bachthyaglx/Stable-Gait-Optimization-for-Small-Sized-Humanoid-Robot-Using-CFO/Solidworks/Part22_1.SLDPRT

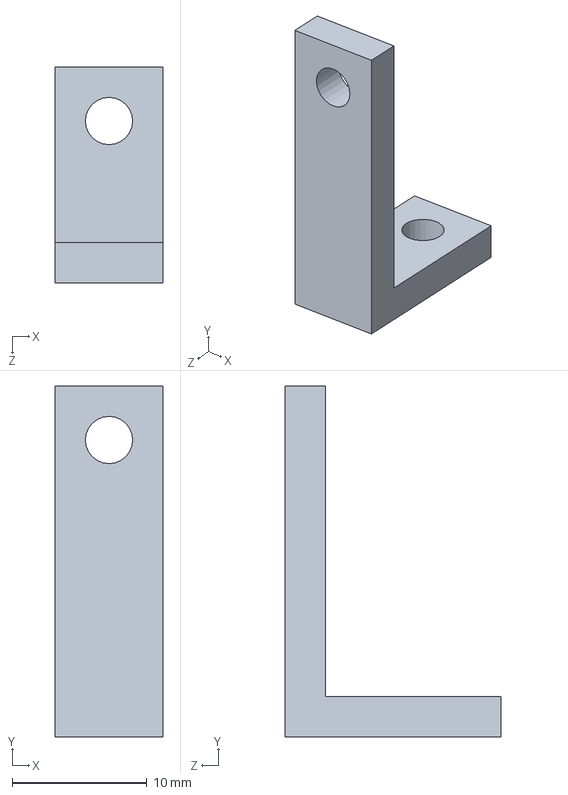
[picture p26: CAD file, 2022-03-02]
Solidworks/Part22_1.SLDPRT
8.00 x 26.0 x 16.0 mm
