bachthyaglx/Stable-Gait-Optimization-for-Small-Sized-Humanoid-Robot-Using-CFO/Solidworks/ArduinoDue/PCB - Arduino.SLDPRT

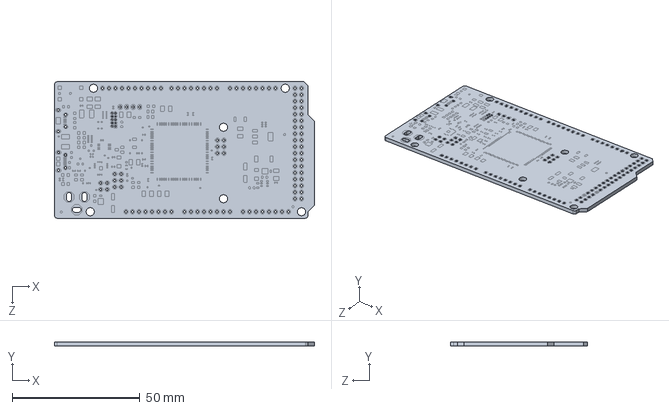
[picture p27: CAD file, 2022-03-02]
Solidworks/ArduinoDue/PCB - Arduino.SLDPRT
101.6 x 1.62 x 53.3 mm
