bachthyaglx/Stable-Gait-Optimization-for-Small-Sized-Humanoid-Robot-Using-CFO/Solidworks/LIPO/NUCLEO.SLDPRT

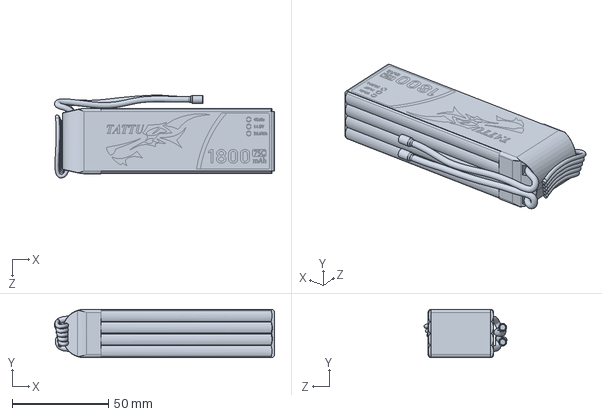
[picture p28: CAD file, 2022-03-02]
Solidworks/LIPO/NUCLEO.SLDPRT
114.2 x 25.0 x 43.0 mm
