bachthyaglx/Stable-Gait-Optimization-for-Small-Sized-Humanoid-Robot-Using-CFO/Solidworks/Part14.SLDPRT

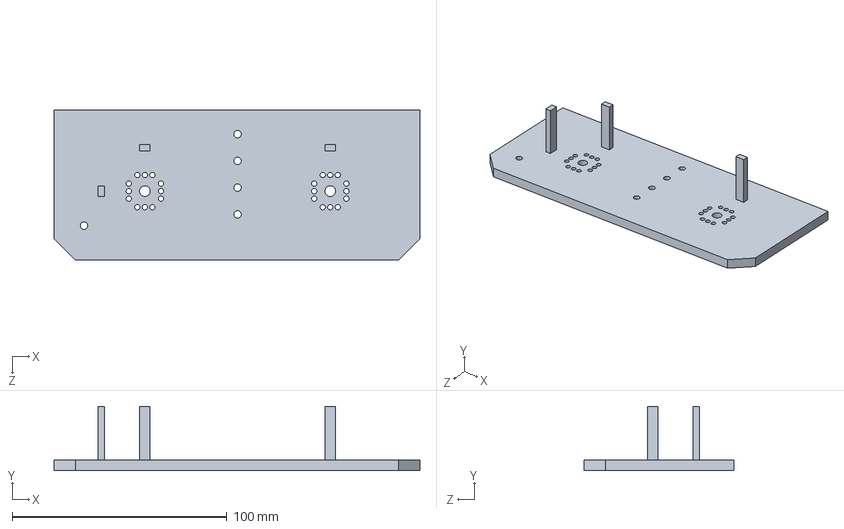
[picture p29: CAD file, 2022-03-02]
Solidworks/Part14.SLDPRT
170.6 x 30.0 x 69.9 mm
