bachthyaglx/Stable-Gait-Optimization-for-Small-Sized-Humanoid-Robot-Using-CFO/Solidworks/LIPO/XT60 Buchse.SLDPRT

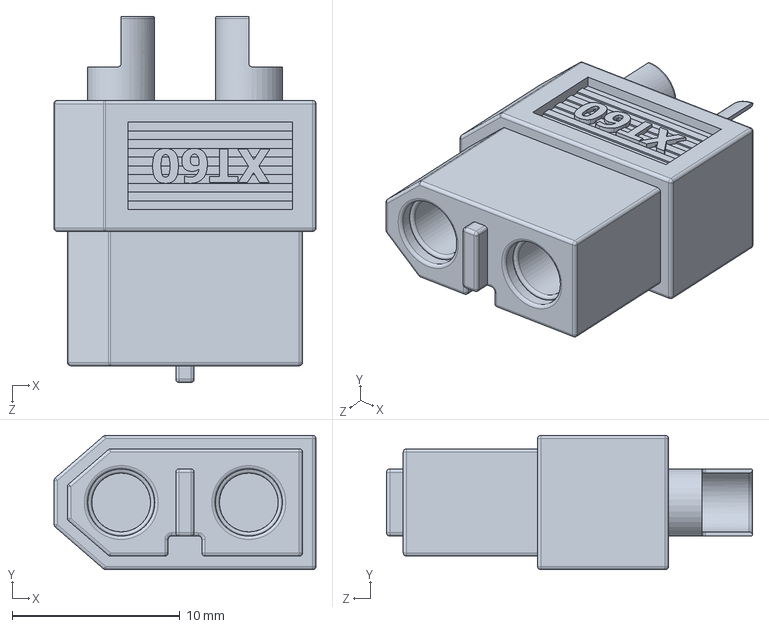
[picture p30: CAD file, 2022-03-02]
Solidworks/LIPO/XT60 Buchse.SLDPRT
15.6 x 8.00 x 21.8 mm
