bachthyaglx/Stable-Gait-Optimization-for-Small-Sized-Humanoid-Robot-Using-CFO/Solidworks/ArduinoDue/Berg Header - 1.27 x 10.SLDPRT

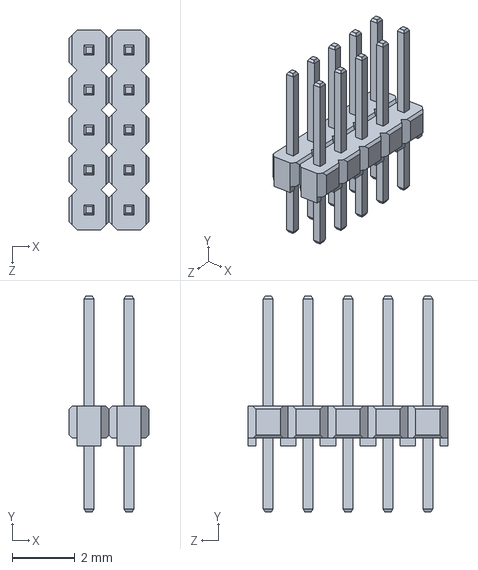
[picture p31: CAD file, 2022-03-02]
Solidworks/ArduinoDue/Berg Header - 1.27 x 10.SLDPRT
2.54 x 6.88 x 6.35 mm
