bachthyaglx/Stable-Gait-Optimization-for-Small-Sized-Humanoid-Robot-Using-CFO/Solidworks/CoDo.SLDPRT

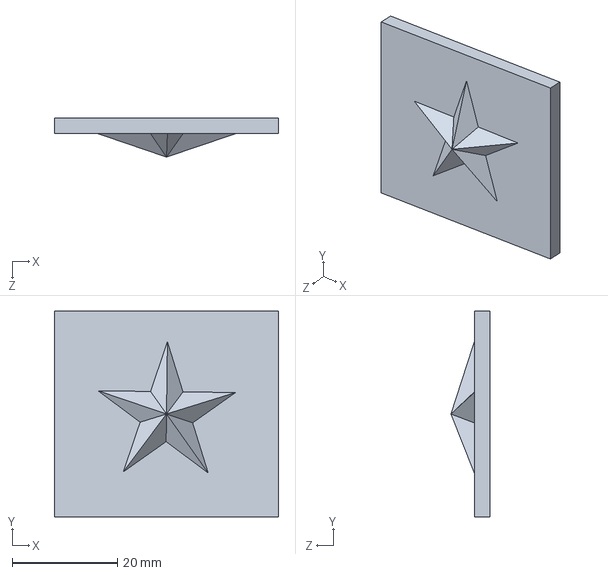
[picture p32: CAD file, 2022-03-02]
Solidworks/CoDo.SLDPRT
42.6 x 39.1 x 7.44 mm
