bachthyaglx/Stable-Gait-Optimization-for-Small-Sized-Humanoid-Robot-Using-CFO/Solidworks/ArduinoDue/MicroUSB AB - Hirose - ZX62D-AB-5P8.SLDPRT

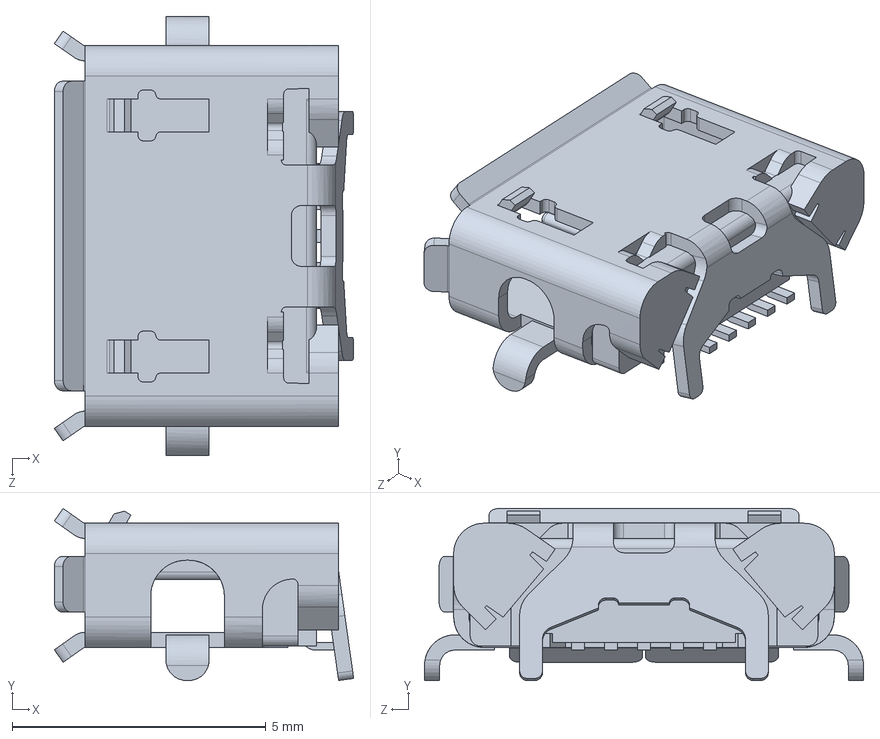
[picture p33: CAD file, 2022-03-02]
Solidworks/ArduinoDue/MicroUSB AB - Hirose - ZX62D-AB-5P8.SLDPRT
5.90 x 3.39 x 8.65 mm
