bachthyaglx/Stable-Gait-Optimization-for-Small-Sized-Humanoid-Robot-Using-CFO/Solidworks/Part15.SLDPRT

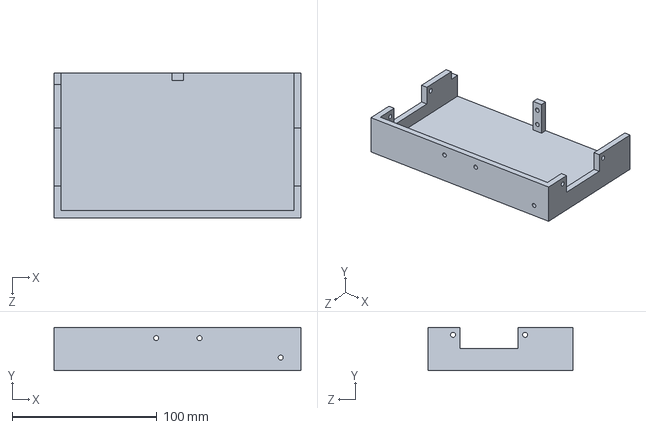
[picture p34: CAD file, 2022-03-02]
Solidworks/Part15.SLDPRT
170.6 x 29.9 x 100.0 mm
