bachthyaglx/Stable-Gait-Optimization-for-Small-Sized-Humanoid-Robot-Using-CFO/Solidworks/ArduinoDue/Capacitor - Nichicon - UUR1C101MCL1GS.SLDPRT

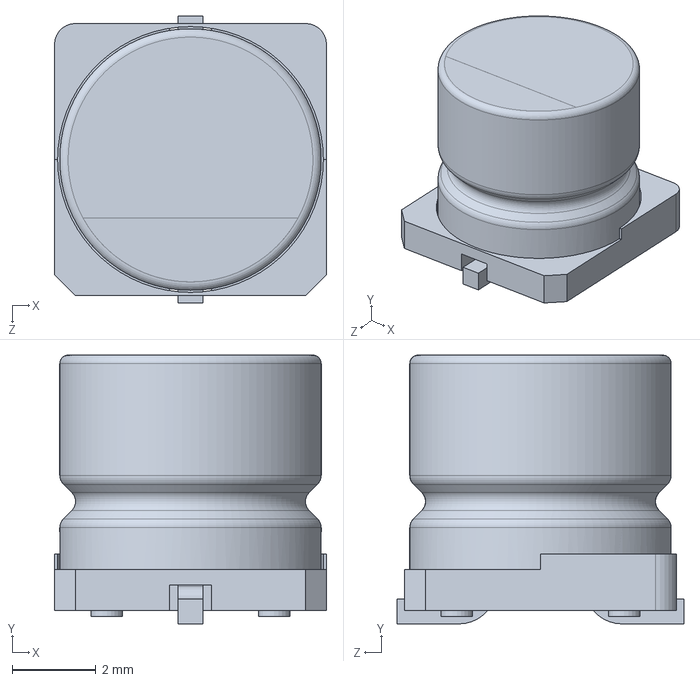
[picture p35: CAD file, 2022-03-02]
Solidworks/ArduinoDue/Capacitor - Nichicon - UUR1C101MCL1GS.SLDPRT
6.50 x 6.42 x 6.85 mm
