bachthyaglx/Stable-Gait-Optimization-for-Small-Sized-Humanoid-Robot-Using-CFO/Solidworks/ArduinoDue/Microchip - Atmel - SAM3X8EAU.SLDPRT

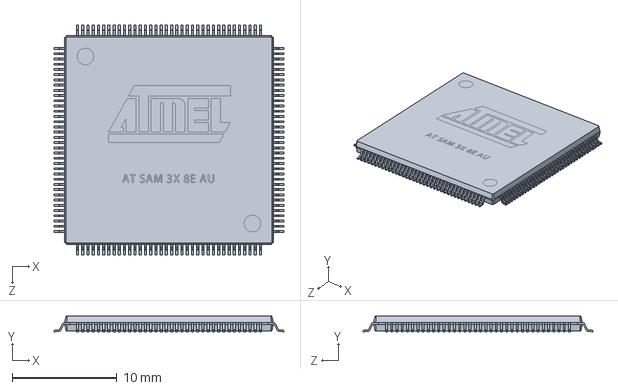
[picture p36: CAD file, 2022-03-02]
Solidworks/ArduinoDue/Microchip - Atmel - SAM3X8EAU.SLDPRT
22.0 x 1.50 x 22.0 mm
