bachthyaglx/Stable-Gait-Optimization-for-Small-Sized-Humanoid-Robot-Using-CFO/Solidworks/Part6.SLDPRT

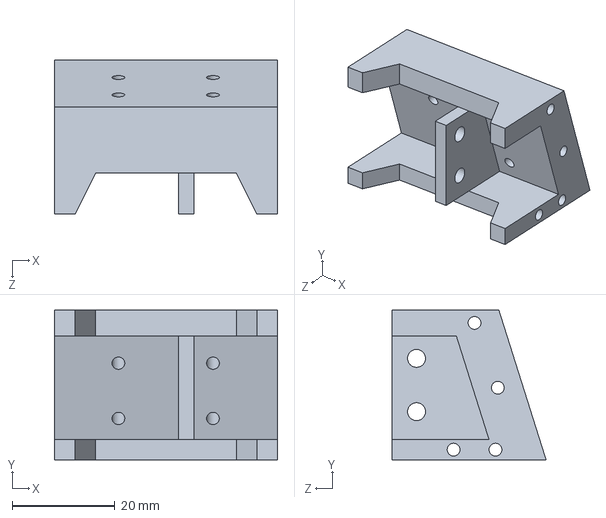
[picture p37: CAD file, 2022-03-02]
Solidworks/Part6.SLDPRT
43.3 x 29.2 x 30.0 mm
