bachthyaglx/Stable-Gait-Optimization-for-Small-Sized-Humanoid-Robot-Using-CFO/Solidworks/ArduinoDue/Power Jack - Kycon - KLDHCX-0202-A.SLDPRT

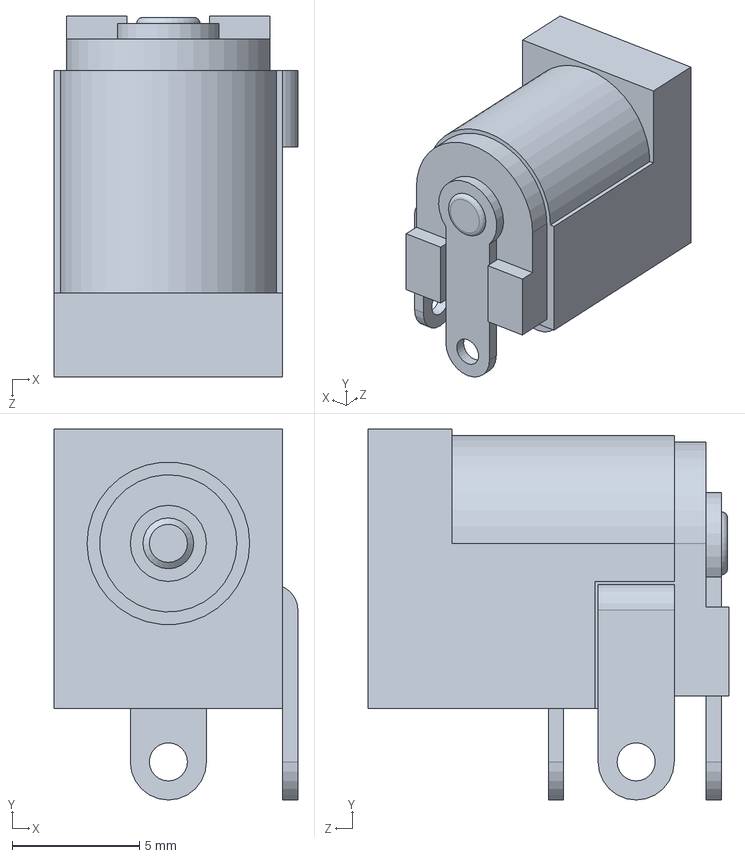
[picture p38: CAD file, 2022-03-02]
Solidworks/ArduinoDue/Power Jack - Kycon - KLDHCX-0202-A.SLDPRT
9.60 x 14.6 x 14.2 mm
