bachthyaglx/Stable-Gait-Optimization-for-Small-Sized-Humanoid-Robot-Using-CFO/Solidworks/ArduinoDue/Berg Header - 2.54 x 2.SLDPRT

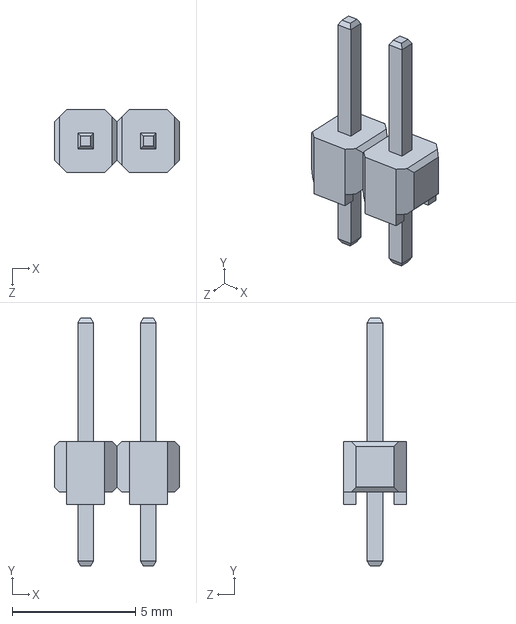
[picture p39: CAD file, 2022-03-02]
Solidworks/ArduinoDue/Berg Header - 2.54 x 2.SLDPRT
5.08 x 10.0 x 2.54 mm
