bachthyaglx/Stable-Gait-Optimization-for-Small-Sized-Humanoid-Robot-Using-CFO/Solidworks/MirrorPart2.SLDPRT

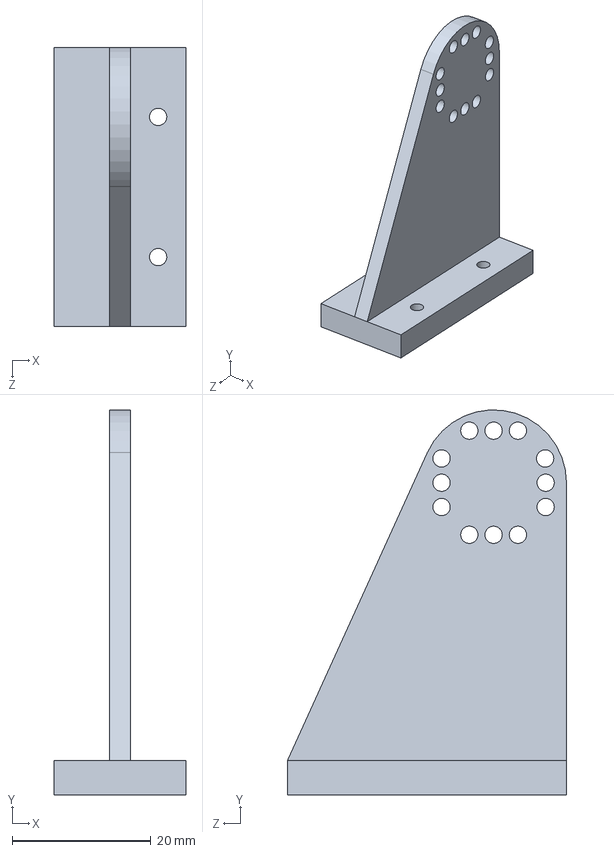
[picture p40: CAD file, 2022-03-02]
Solidworks/MirrorPart2.SLDPRT
19.0 x 55.5 x 40.2 mm
