bachthyaglx/Stable-Gait-Optimization-for-Small-Sized-Humanoid-Robot-Using-CFO/Solidworks/ArduinoDue/LED - Kingbright - KPT-3216EC.SLDPRT

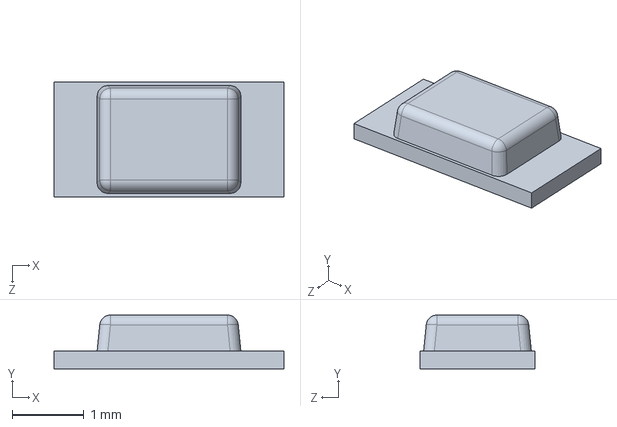
[picture p41: CAD file, 2022-03-02]
Solidworks/ArduinoDue/LED - Kingbright - KPT-3216EC.SLDPRT
3.20 x 0.75 x 1.60 mm
