bachthyaglx/Stable-Gait-Optimization-for-Small-Sized-Humanoid-Robot-Using-CFO/Solidworks/Part21.SLDPRT

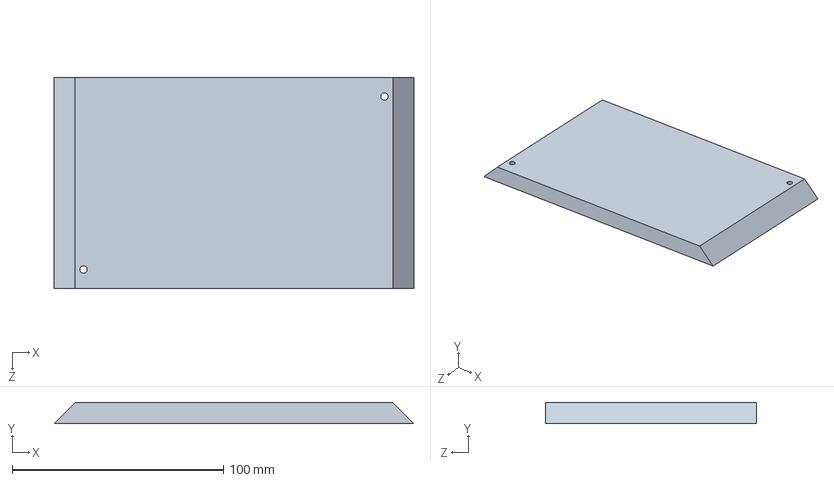
[picture p42: CAD file, 2022-03-02]
Solidworks/Part21.SLDPRT
170.6 x 10.0 x 100.0 mm
