bachthyaglx/Stable-Gait-Optimization-for-Small-Sized-Humanoid-Robot-Using-CFO/Solidworks/ArduinoDue/MicroUSB AB - Hirose - ZX62-AB-5PA.SLDPRT

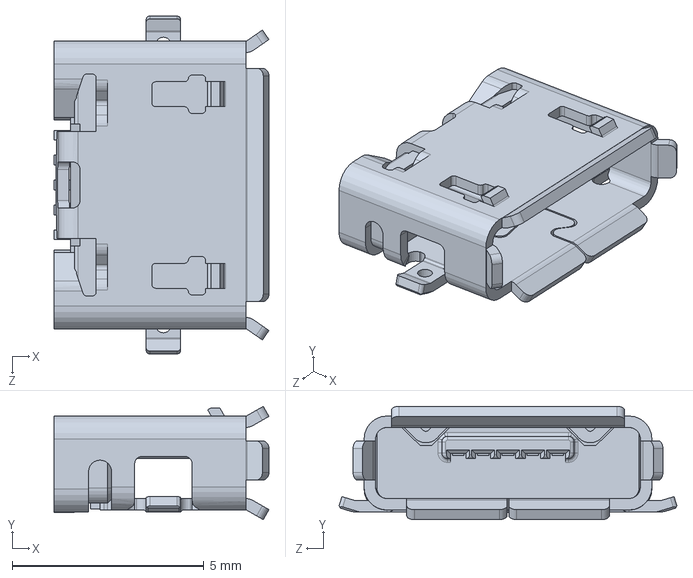
[picture p43: CAD file, 2022-03-02]
Solidworks/ArduinoDue/MicroUSB AB - Hirose - ZX62-AB-5PA.SLDPRT
5.60 x 2.95 x 8.80 mm
