bachthyaglx/Stable-Gait-Optimization-for-Small-Sized-Humanoid-Robot-Using-CFO/Solidworks/Servo Output Shaft.SLDPRT

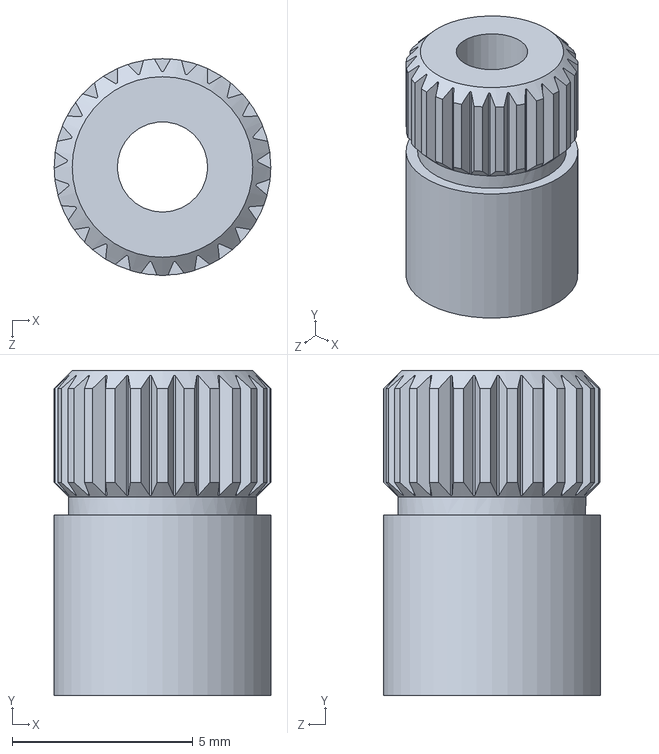
[picture p44: CAD file, 2022-03-02]
Solidworks/Servo Output Shaft.SLDPRT
6.00 x 9.00 x 6.00 mm
