bachthyaglx/Stable-Gait-Optimization-for-Small-Sized-Humanoid-Robot-Using-CFO/Solidworks/ArduinoDue/Switch - ESwitch - TLE3303.SLDPRT

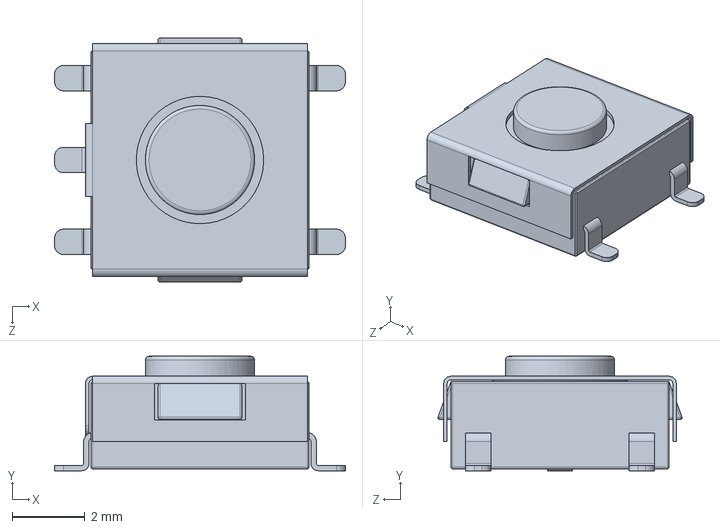
[picture p45: CAD file, 2022-03-02]
Solidworks/ArduinoDue/Switch - ESwitch - TLE3303.SLDPRT
8.00 x 3.15 x 6.71 mm
