bachthyaglx/Stable-Gait-Optimization-for-Small-Sized-Humanoid-Robot-Using-CFO/Solidworks/HandShake.SLDPRT

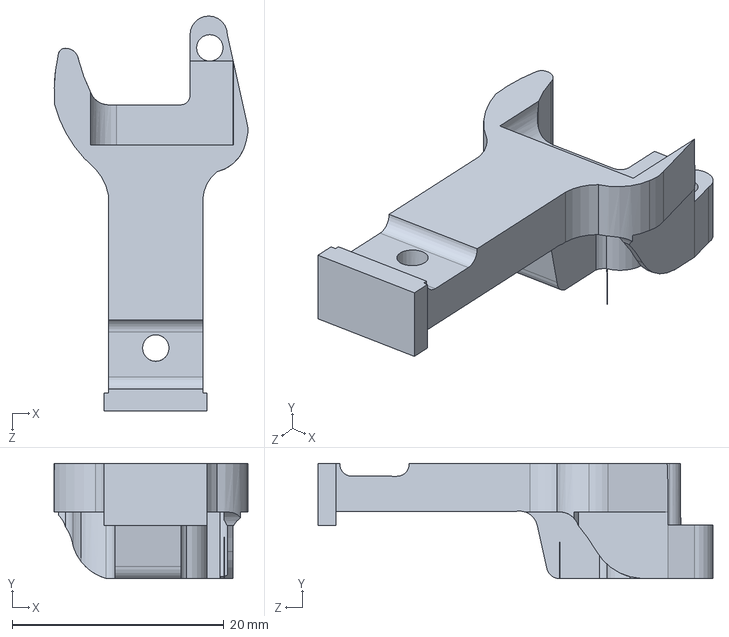
[picture p46: CAD file, 2022-03-02]
Solidworks/HandShake.SLDPRT
18.3 x 10.9 x 37.3 mm
