bachthyaglx/Stable-Gait-Optimization-for-Small-Sized-Humanoid-Robot-Using-CFO/Solidworks/ArduinoDue/Capacitor.SLDPRT

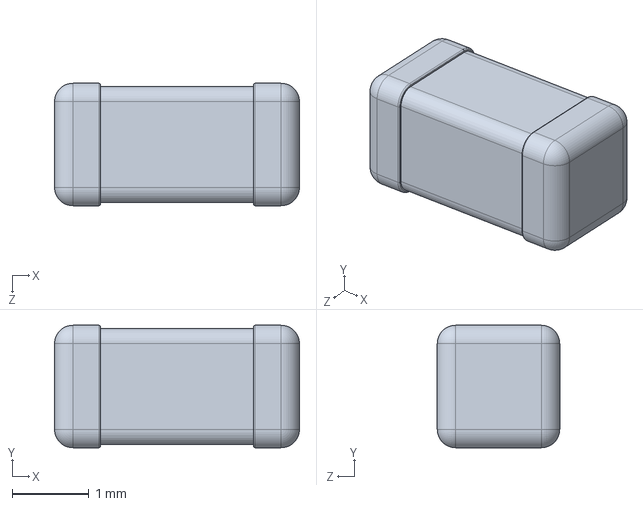
[picture p47: CAD file, 2022-03-02]
Solidworks/ArduinoDue/Capacitor.SLDPRT
3.20 x 1.60 x 1.60 mm
