bachthyaglx/Stable-Gait-Optimization-for-Small-Sized-Humanoid-Robot-Using-CFO/Solidworks/TruongSa.SLDPRT

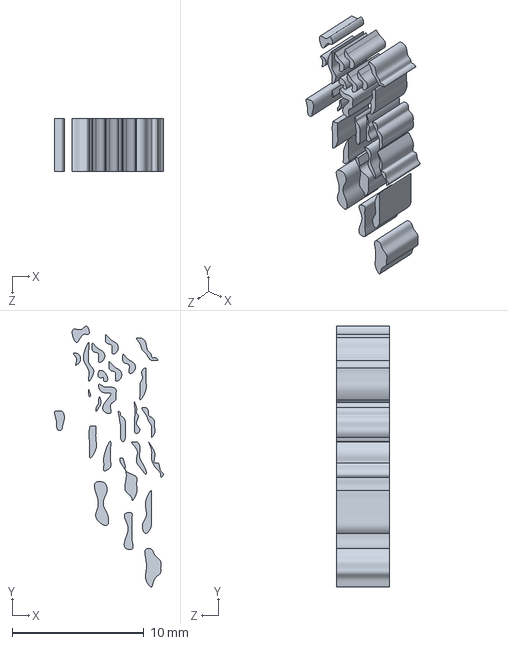
[picture p48: CAD file, 2022-03-02]
Solidworks/TruongSa.SLDPRT
8.27 x 19.8 x 4.00 mm
