bachthyaglx/Stable-Gait-Optimization-for-Small-Sized-Humanoid-Robot-Using-CFO/Solidworks/ArduinoDue/Berg Header Receptacle 2.54 x 36 - FCI - 66953-018LF.SLDPRT

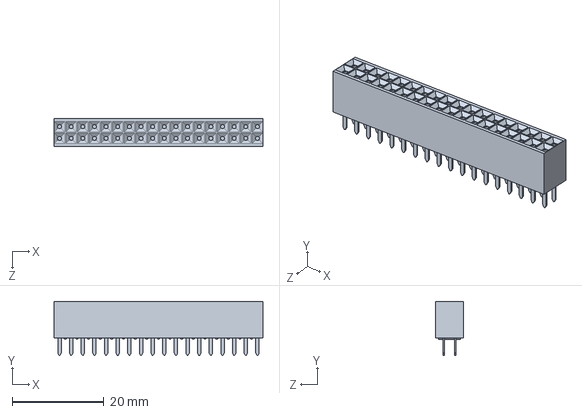
[picture p49: CAD file, 2022-03-02]
Solidworks/ArduinoDue/Berg Header Receptacle 2.54 x 36 - FCI - 66953-018LF.SLDPRT
45.6 x 11.8 x 6.10 mm
