bachthyaglx/Stable-Gait-Optimization-for-Small-Sized-Humanoid-Robot-Using-CFO/Solidworks/CoVang.SLDPRT

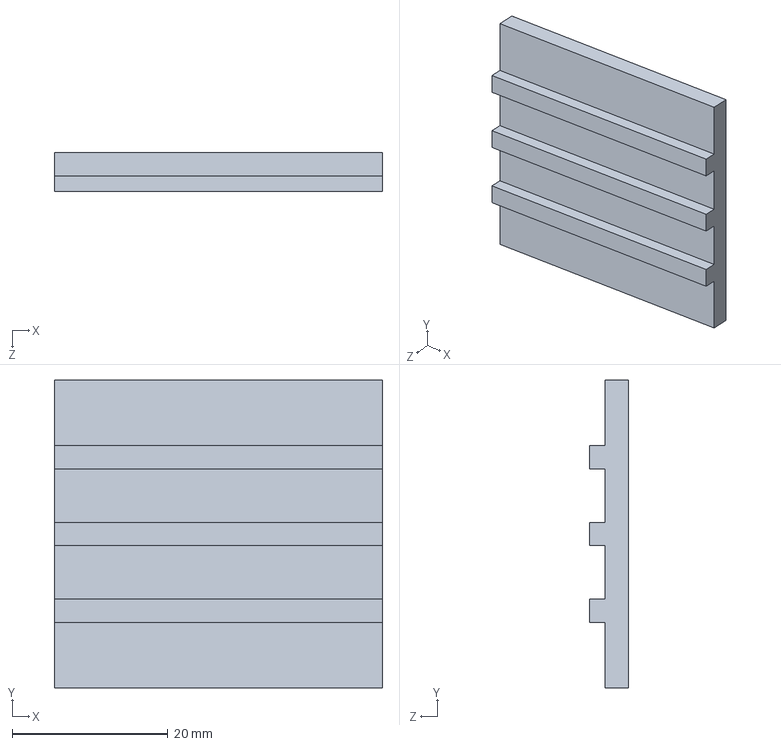
[picture p50: CAD file, 2022-03-02]
Solidworks/CoVang.SLDPRT
42.1 x 39.5 x 5.00 mm
