bachthyaglx/Stable-Gait-Optimization-for-Small-Sized-Humanoid-Robot-Using-CFO/Solidworks/Banhrang.SLDPRT

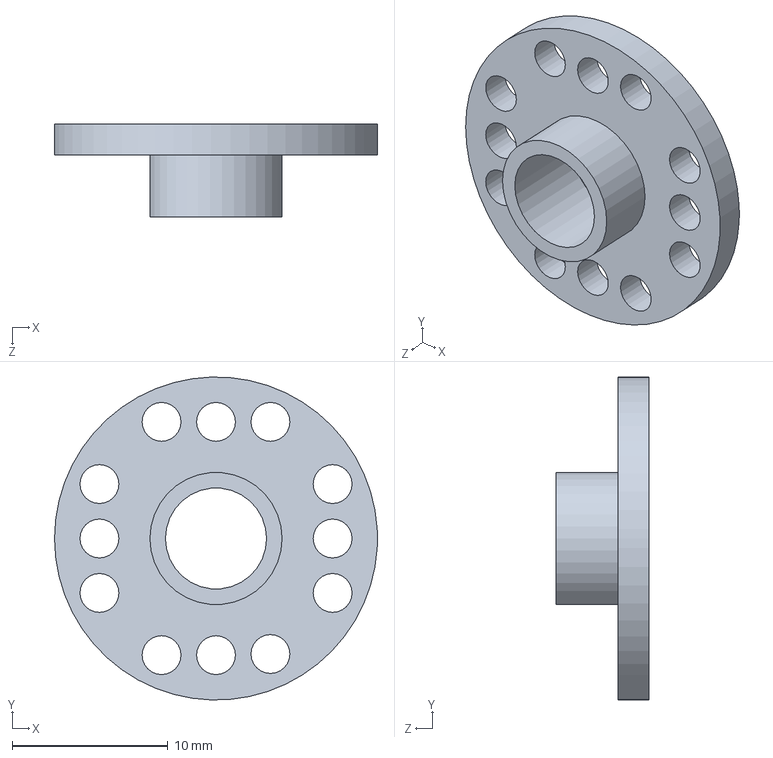
[picture p51: CAD file, 2022-03-02]
Solidworks/Banhrang.SLDPRT
20.8 x 20.8 x 6.00 mm
