bachthyaglx/Stable-Gait-Optimization-for-Small-Sized-Humanoid-Robot-Using-CFO/Solidworks/Part22.SLDPRT

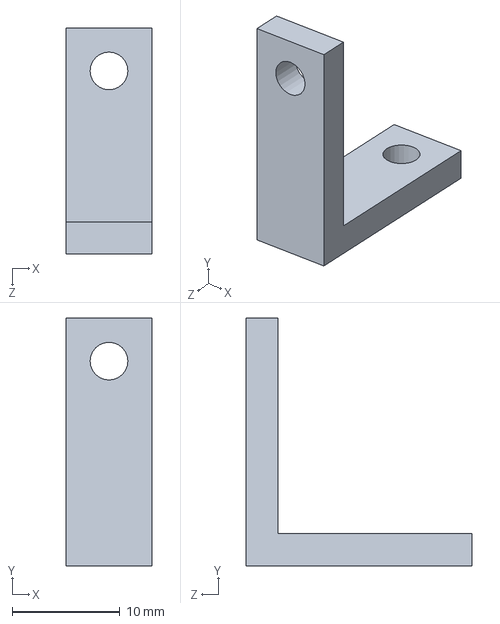
[picture p52: CAD file, 2022-03-02]
Solidworks/Part22.SLDPRT
8.00 x 23.0 x 21.0 mm
