bachthyaglx/Stable-Gait-Optimization-for-Small-Sized-Humanoid-Robot-Using-CFO/Solidworks/Mirror_Part3.SLDPRT

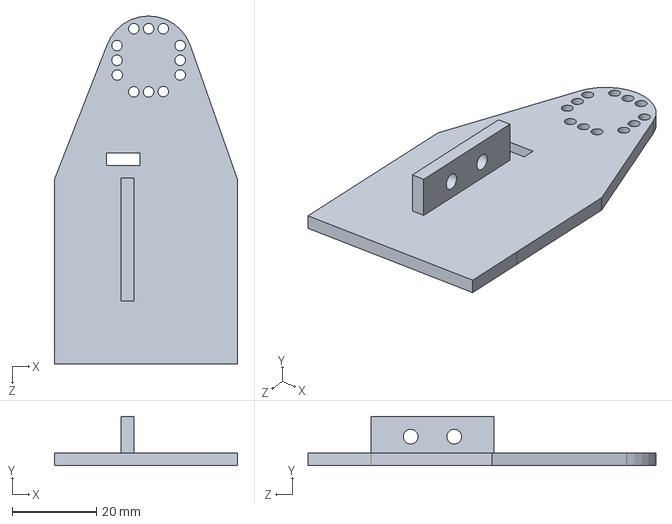
[picture p53: CAD file, 2022-03-02]
Solidworks/Mirror_Part3.SLDPRT
43.6 x 11.7 x 82.6 mm
