bachthyaglx/Stable-Gait-Optimization-for-Small-Sized-Humanoid-Robot-Using-CFO/Solidworks/Part20_KhopTay.SLDPRT

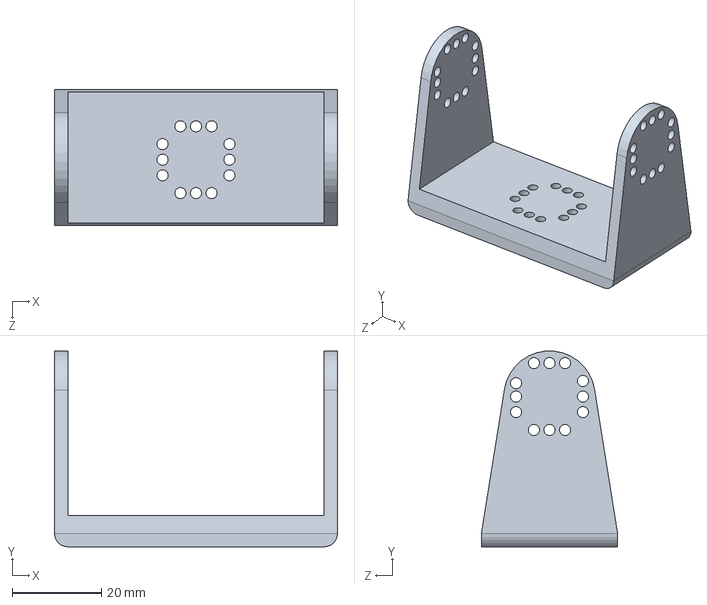
[picture p54: CAD file, 2022-03-02]
Solidworks/Part20_KhopTay.SLDPRT
63.5 x 43.9 x 30.6 mm
