bachthyaglx/Stable-Gait-Optimization-for-Small-Sized-Humanoid-Robot-Using-CFO/Solidworks/VietNam.SLDPRT

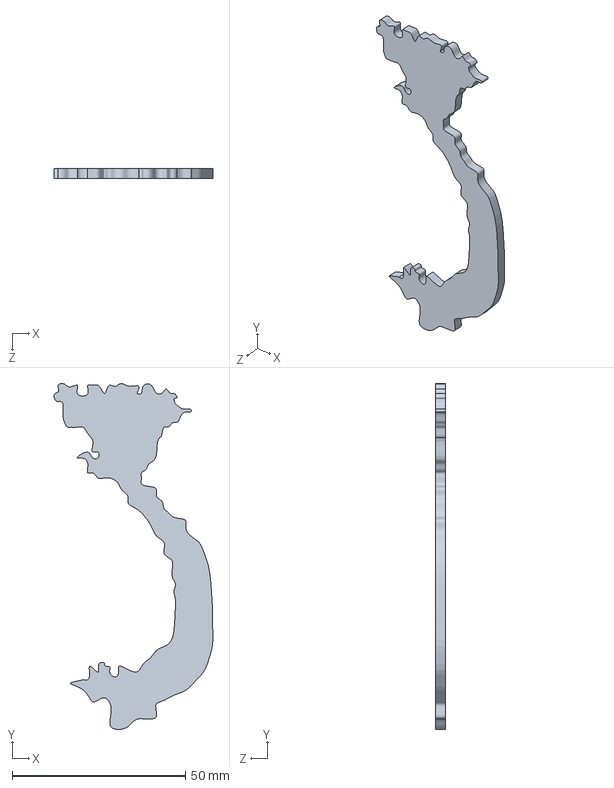
[picture p55: CAD file, 2022-03-02]
Solidworks/VietNam.SLDPRT
45.8 x 99.8 x 3.00 mm
