bachthyaglx/Stable-Gait-Optimization-for-Small-Sized-Humanoid-Robot-Using-CFO/Solidworks/DAYDIEN.SLDPRT

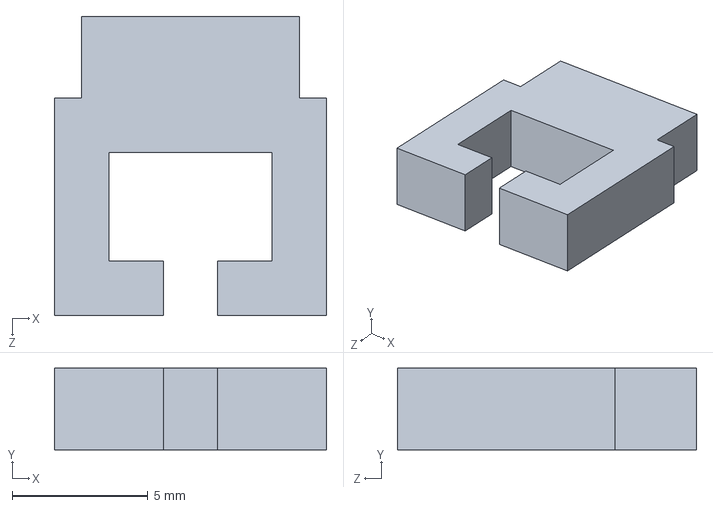
[picture p56: CAD file, 2022-03-02]
Solidworks/DAYDIEN.SLDPRT
10.0 x 3.00 x 11.0 mm
