bachthyaglx/Stable-Gait-Optimization-for-Small-Sized-Humanoid-Robot-Using-CFO/Solidworks/Part5.SLDPRT

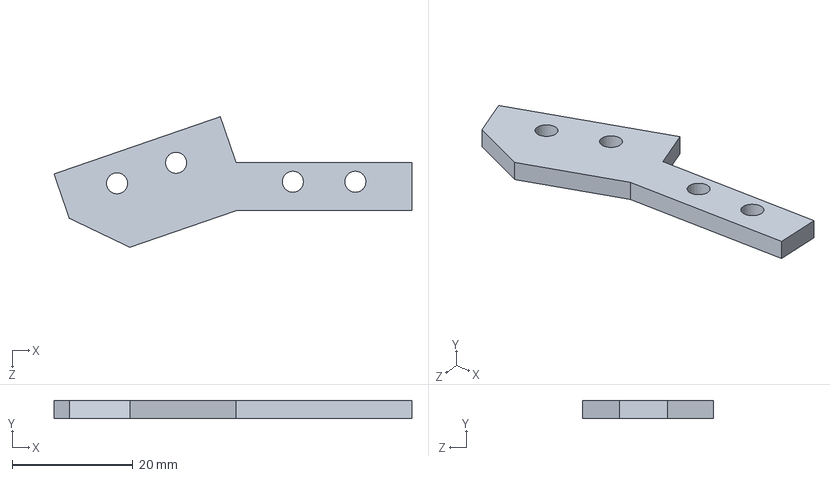
[picture p57: CAD file, 2022-03-02]
Solidworks/Part5.SLDPRT
59.3 x 3.00 x 21.6 mm
