bachthyaglx/Stable-Gait-Optimization-for-Small-Sized-Humanoid-Robot-Using-CFO/Solidworks/Part9.SLDPRT

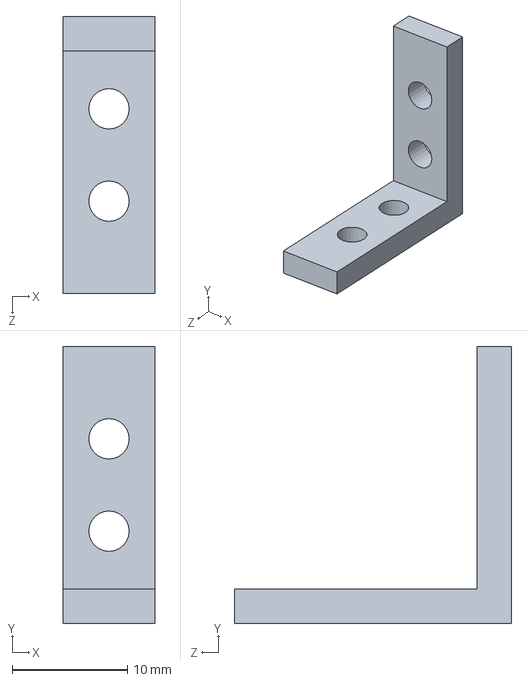
[picture p58: CAD file, 2022-03-02]
Solidworks/Part9.SLDPRT
8.00 x 24.0 x 24.0 mm
