bachthyaglx/Stable-Gait-Optimization-for-Small-Sized-Humanoid-Robot-Using-CFO/Solidworks/Part19.SLDPRT

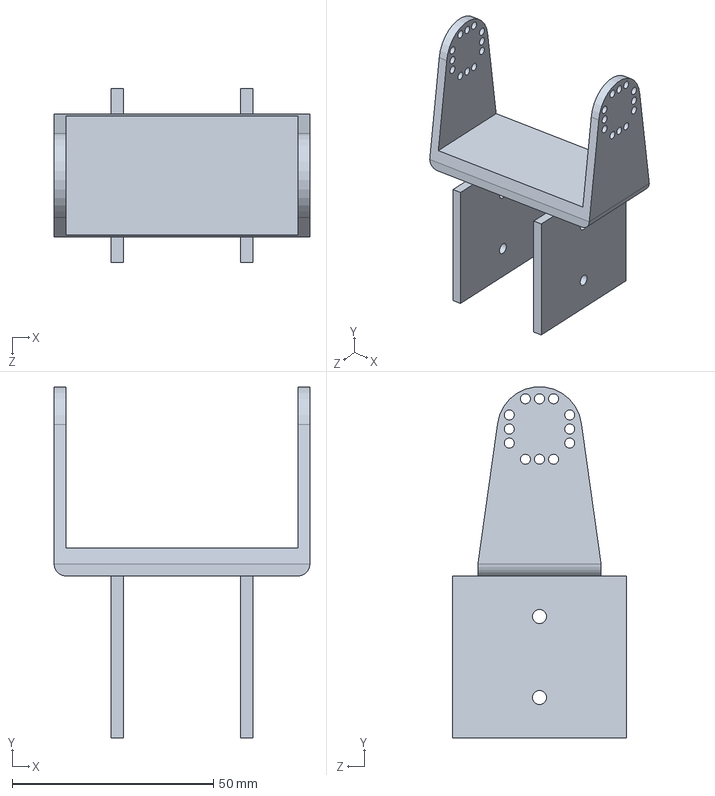
[picture p59: CAD file, 2022-03-02]
Solidworks/Part19.SLDPRT
63.5 x 87.1 x 43.1 mm
