bachthyaglx/Stable-Gait-Optimization-for-Small-Sized-Humanoid-Robot-Using-CFO/Solidworks/Part8.SLDPRT

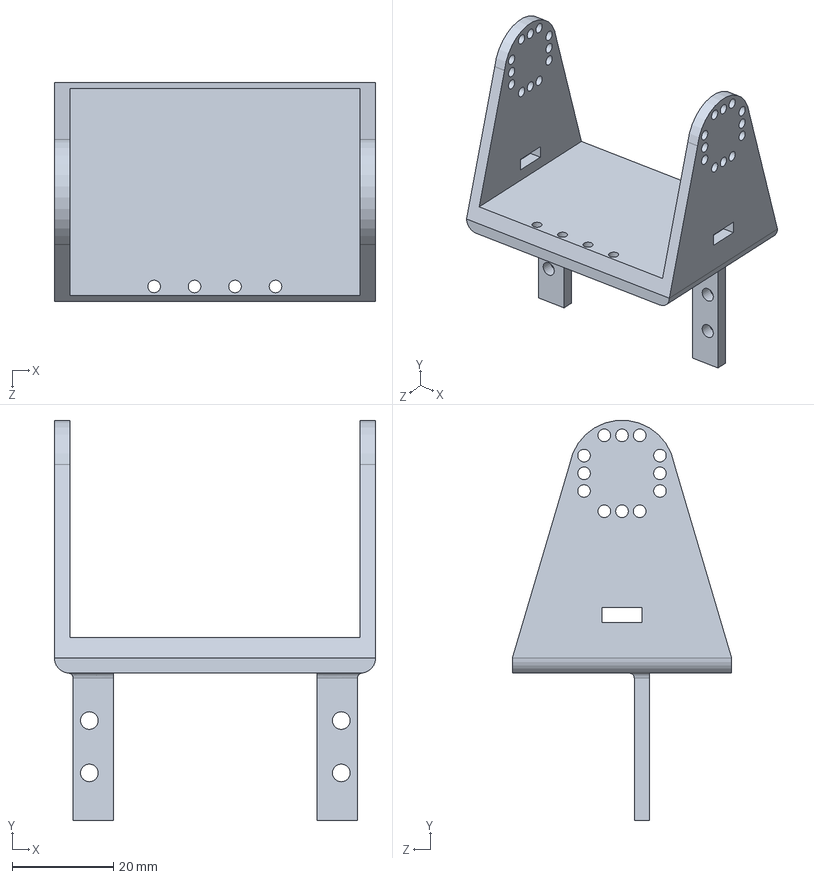
[picture p60: CAD file, 2022-03-02]
Solidworks/Part8.SLDPRT
63.5 x 79.1 x 43.4 mm
