bachthyaglx/Stable-Gait-Optimization-for-Small-Sized-Humanoid-Robot-Using-CFO/Solidworks/Khophong.SLDPRT

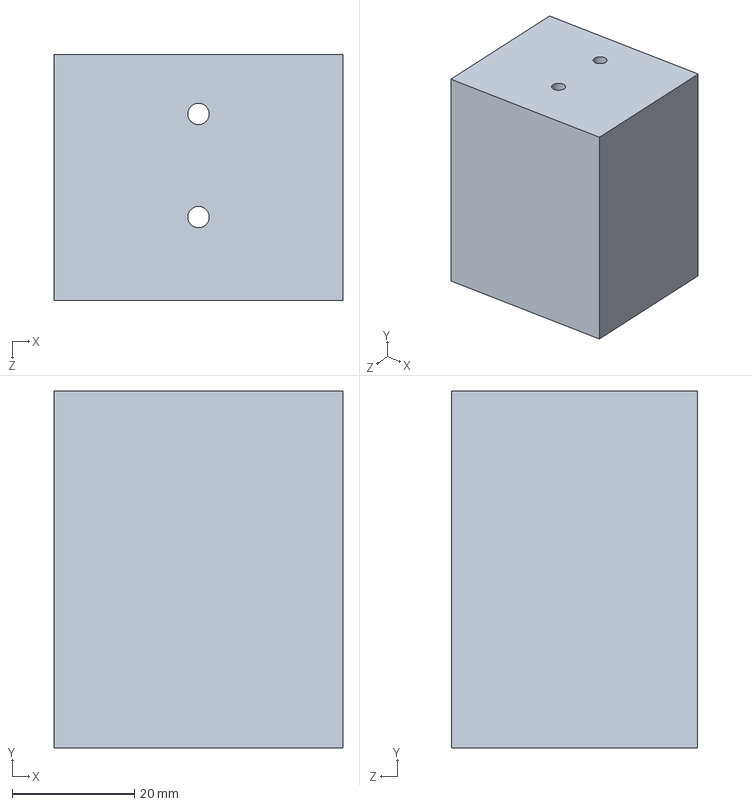
[picture p61: CAD file, 2022-03-02]
Solidworks/Khophong.SLDPRT
47.3 x 58.4 x 40.2 mm
