bachthyaglx/Stable-Gait-Optimization-for-Small-Sized-Humanoid-Robot-Using-CFO/Solidworks/Mirror_Part7.SLDPRT

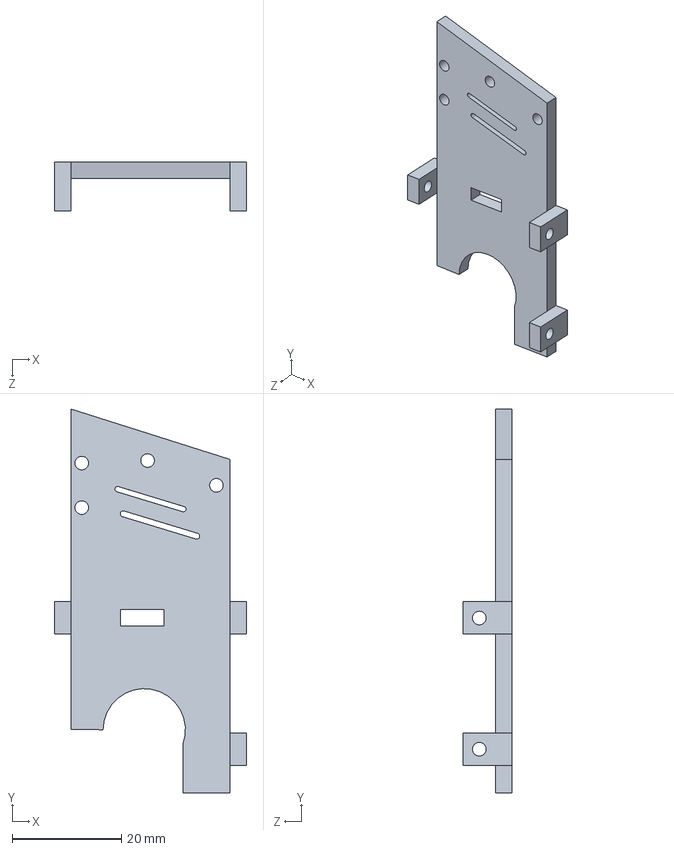
[picture p62: CAD file, 2022-03-02]
Solidworks/Mirror_Part7.SLDPRT
35.1 x 70.2 x 9.00 mm
