bachthyaglx/Stable-Gait-Optimization-for-Small-Sized-Humanoid-Robot-Using-CFO/Solidworks/Standard Servo (1501MG).SLDPRT

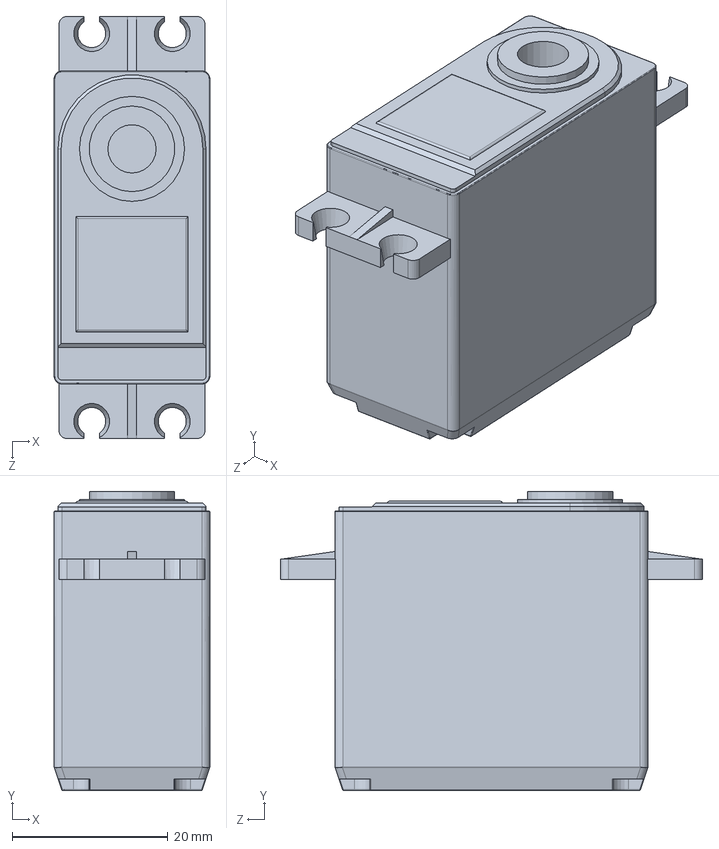
[picture p63: CAD file, 2022-03-02]
Solidworks/Standard Servo (1501MG).SLDPRT
20.0 x 38.4 x 54.2 mm
