bachthyaglx/Stable-Gait-Optimization-for-Small-Sized-Humanoid-Robot-Using-CFO/Solidworks/Part11_2.SLDPRT

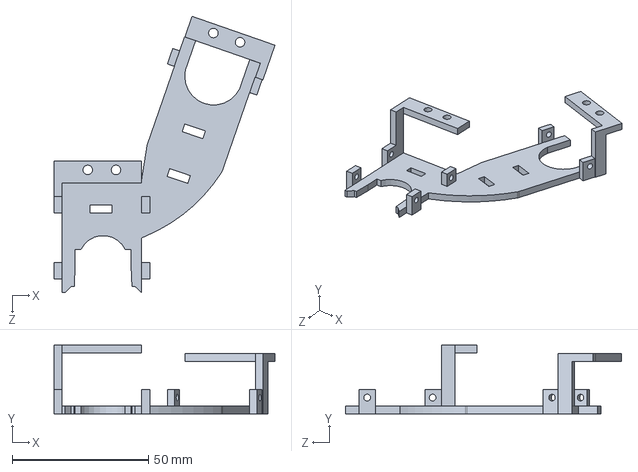
[picture p64: CAD file, 2022-03-02]
Solidworks/Part11_2.SLDPRT
81.0 x 25.2 x 101.3 mm
