bachthyaglx/Stable-Gait-Optimization-for-Small-Sized-Humanoid-Robot-Using-CFO/Solidworks/HoangSa.SLDPRT

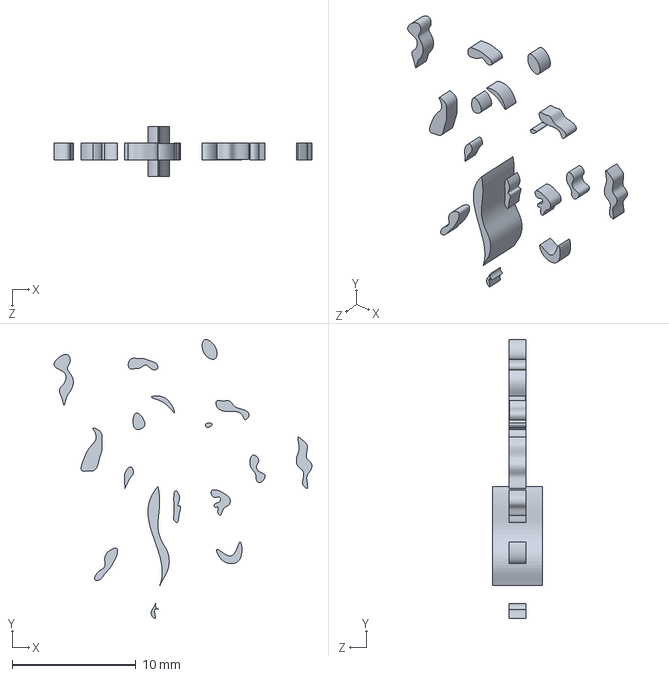
[picture p65: CAD file, 2022-03-02]
Solidworks/HoangSa.SLDPRT
20.8 x 22.5 x 4.00 mm
