bachthyaglx/Stable-Gait-Optimization-for-Small-Sized-Humanoid-Robot-Using-CFO/Solidworks/Part1.SLDPRT

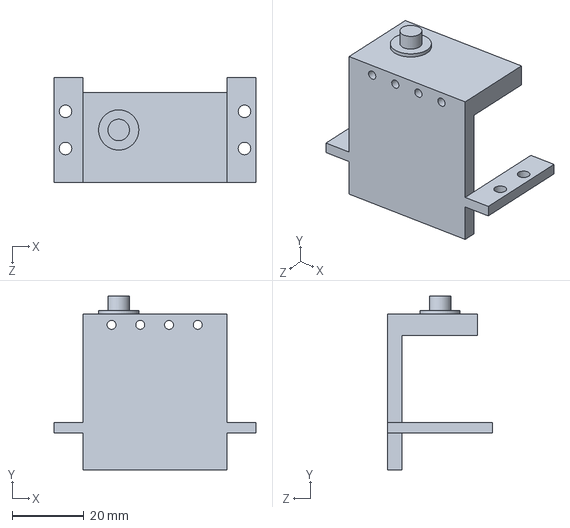
[picture p66: CAD file, 2022-03-02]
Solidworks/Part1.SLDPRT
56.2 x 48.4 x 29.1 mm
