bachthyaglx/Stable-Gait-Optimization-for-Small-Sized-Humanoid-Robot-Using-CFO/Solidworks/DAU.SLDPRT

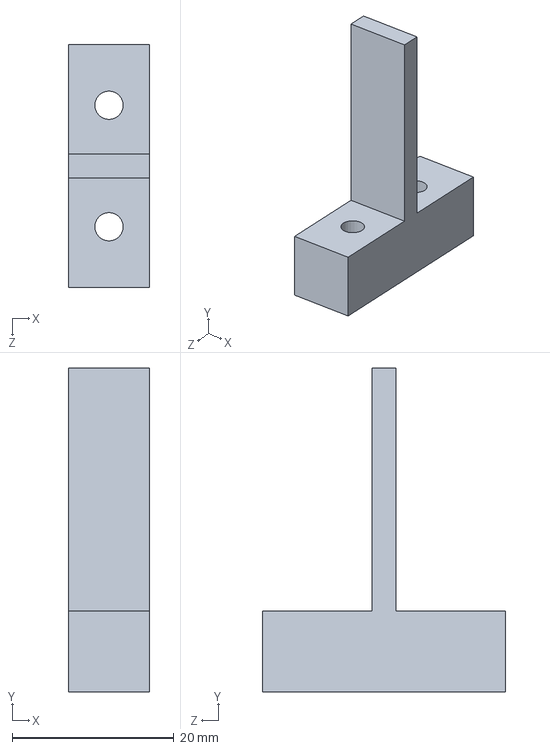
[picture p67: CAD file, 2022-03-02]
Solidworks/DAU.SLDPRT
10.00 x 40.0 x 30.0 mm
