bachthyaglx/Stable-Gait-Optimization-for-Small-Sized-Humanoid-Robot-Using-CFO/Solidworks/Part12_1.SLDPRT

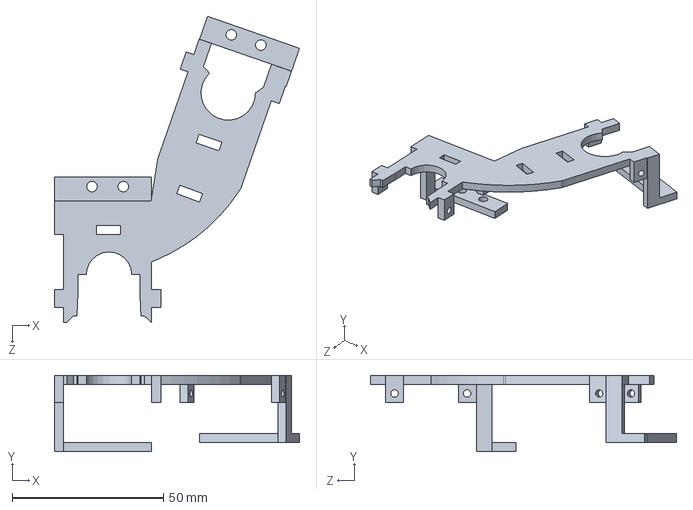
[picture p68: CAD file, 2022-03-02]
Solidworks/Part12_1.SLDPRT
81.0 x 25.2 x 101.3 mm
