bachthyaglx/Stable-Gait-Optimization-for-Small-Sized-Humanoid-Robot-Using-CFO/Solidworks/Banchan.SLDPRT

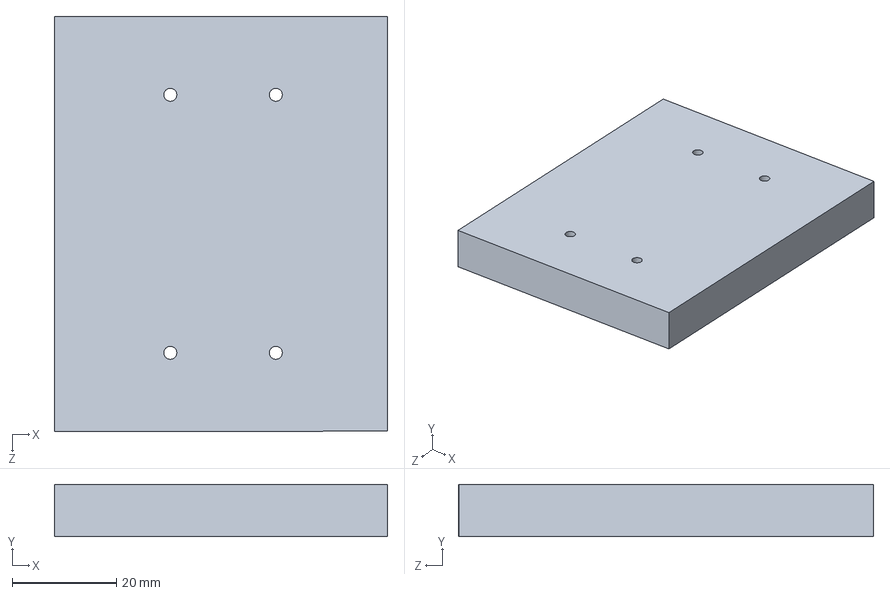
[picture p69: CAD file, 2022-03-02]
Solidworks/Banchan.SLDPRT
63.8 x 10.0 x 79.5 mm
