bachthyaglx/Stable-Gait-Optimization-for-Small-Sized-Humanoid-Robot-Using-CFO/Solidworks/Part11_1.SLDPRT

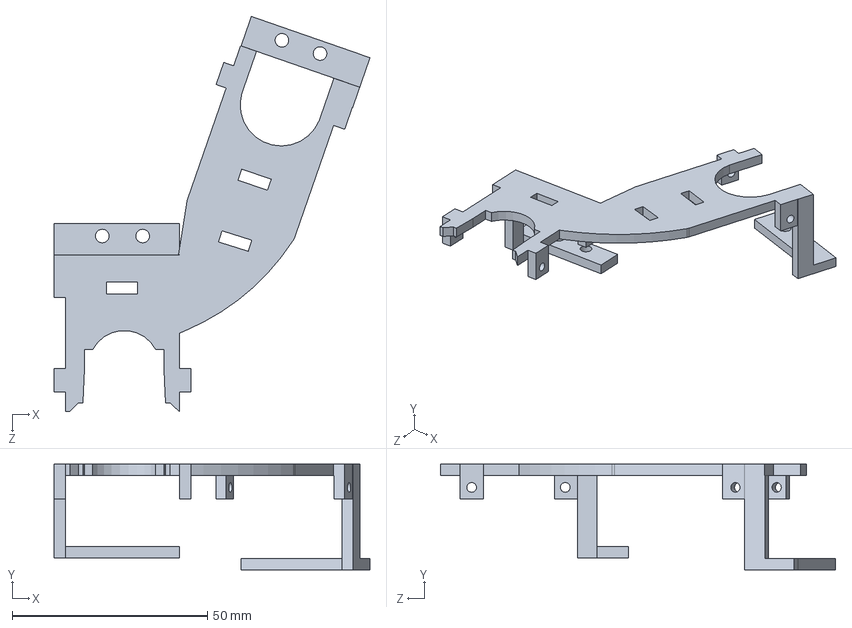
[picture p70: CAD file, 2022-03-02]
Solidworks/Part11_1.SLDPRT
81.0 x 27.2 x 101.3 mm
