bachthyaglx/Stable-Gait-Optimization-for-Small-Sized-Humanoid-Robot-Using-CFO/Solidworks/Part4.SLDPRT

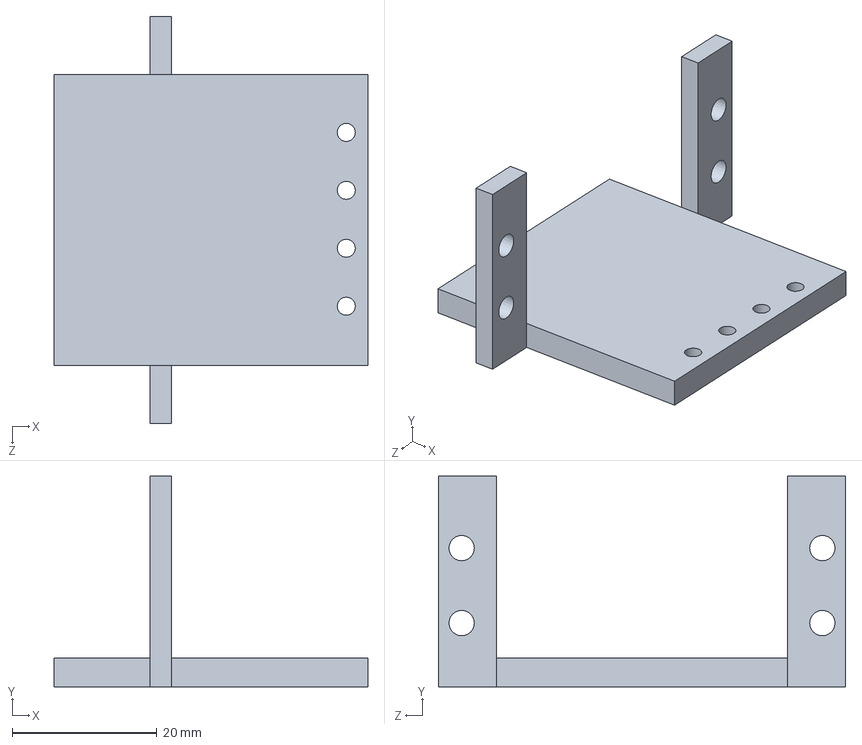
[picture p71: CAD file, 2022-03-02]
Solidworks/Part4.SLDPRT
43.3 x 29.1 x 56.2 mm
