bachthyaglx/Stable-Gait-Optimization-for-Small-Sized-Humanoid-Robot-Using-CFO/Solidworks/Part12_2.SLDPRT

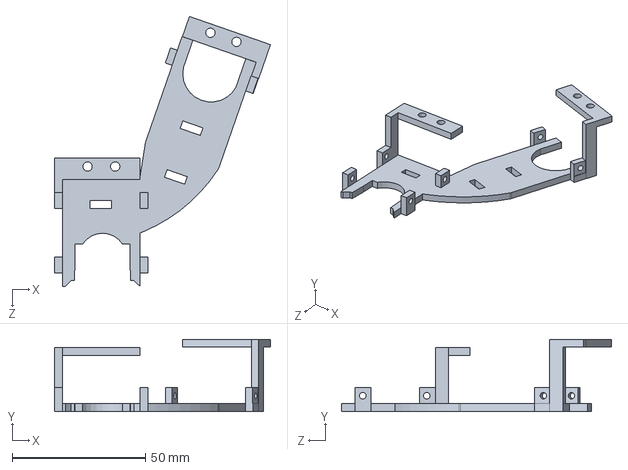
[picture p72: CAD file, 2022-03-02]
Solidworks/Part12_2.SLDPRT
81.0 x 27.2 x 101.3 mm
