bachthyaglx/Stable-Gait-Optimization-for-Small-Sized-Humanoid-Robot-Using-CFO/Solidworks/DAU_1.SLDPRT

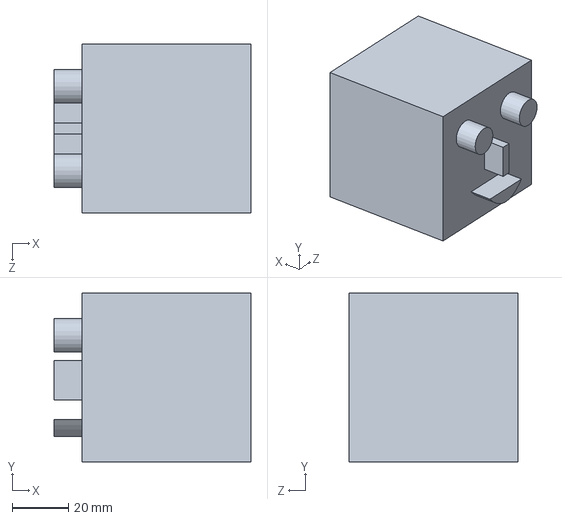
[picture p73: CAD file, 2022-03-02]
Solidworks/DAU_1.SLDPRT
69.9 x 59.9 x 59.9 mm
