bachthyaglx/Stable-Gait-Optimization-for-Small-Sized-Humanoid-Robot-Using-CFO/Solidworks/Part17.SLDPRT

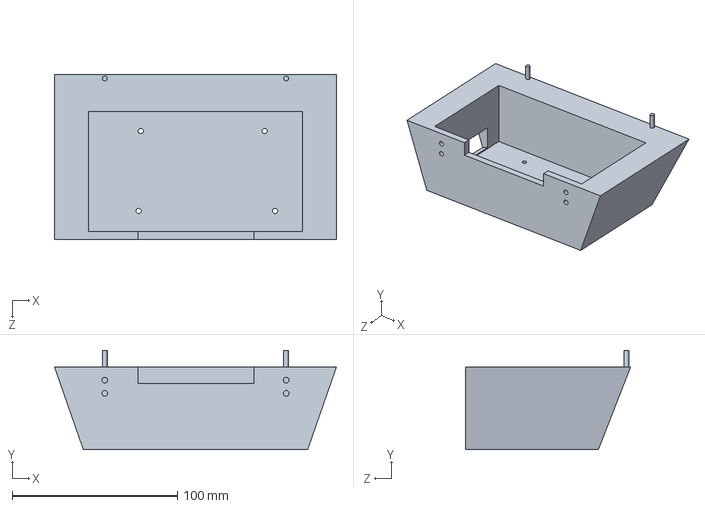
[picture p74: CAD file, 2022-03-02]
Solidworks/Part17.SLDPRT
170.6 x 60.0 x 100.0 mm
