bachthyaglx/Stable-Gait-Optimization-for-Small-Sized-Humanoid-Robot-Using-CFO/Solidworks/Part16.SLDPRT

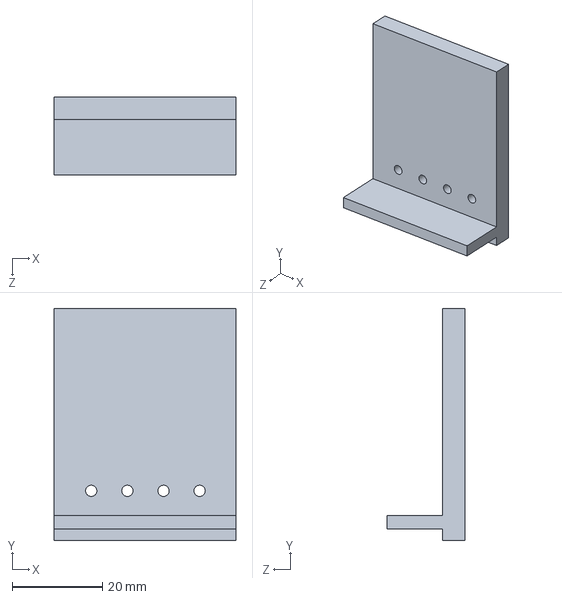
[picture p75: CAD file, 2022-03-02]
Solidworks/Part16.SLDPRT
40.2 x 51.3 x 17.3 mm
