bachthyaglx/Stable-Gait-Optimization-for-Small-Sized-Humanoid-Robot-Using-CFO/Solidworks/Part18.SLDPRT

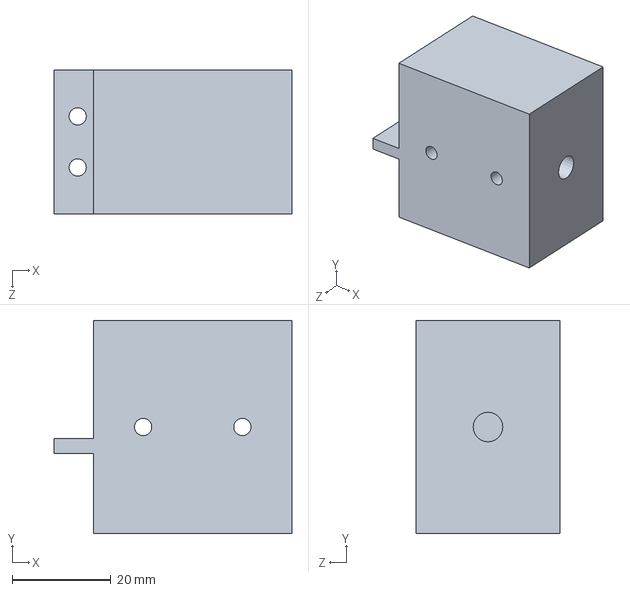
[picture p76: CAD file, 2022-03-02]
Solidworks/Part18.SLDPRT
48.2 x 43.1 x 29.1 mm
