bachthyaglx/Stable-Gait-Optimization-for-Small-Sized-Humanoid-Robot-Using-CFO/Solidworks/Part1_67.SLDPRT

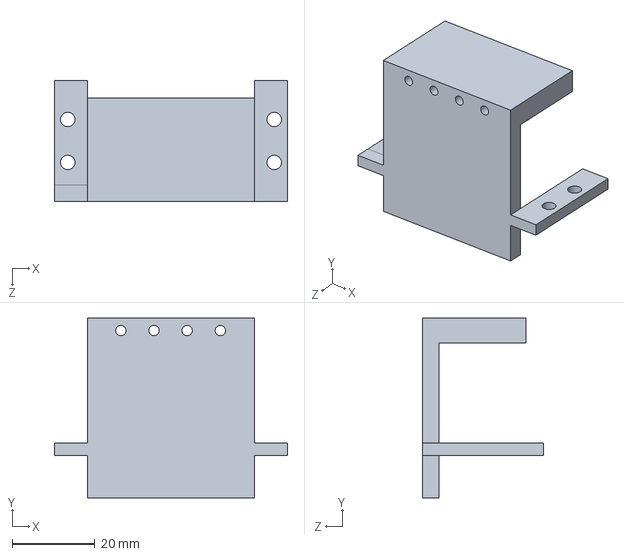
[picture p77: CAD file, 2022-03-02]
Solidworks/Part1_67.SLDPRT
56.2 x 43.4 x 29.1 mm
