bachthyaglx/Stable-Gait-Optimization-for-Small-Sized-Humanoid-Robot-Using-CFO/Solidworks/Part10.SLDPRT

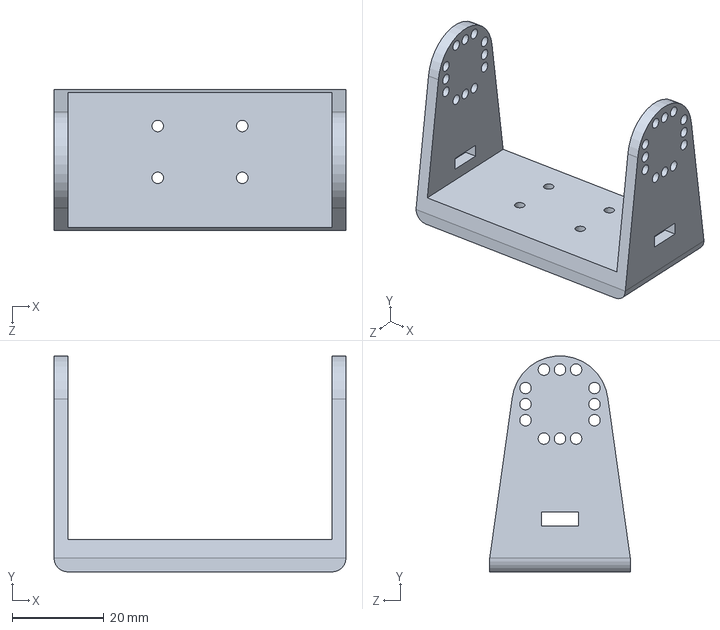
[picture p79: CAD file, 2022-03-02]
Solidworks/Part10.SLDPRT
63.5 x 47.0 x 30.6 mm
